Gueni/BLE-NTC/3D/00019202.SLDASM

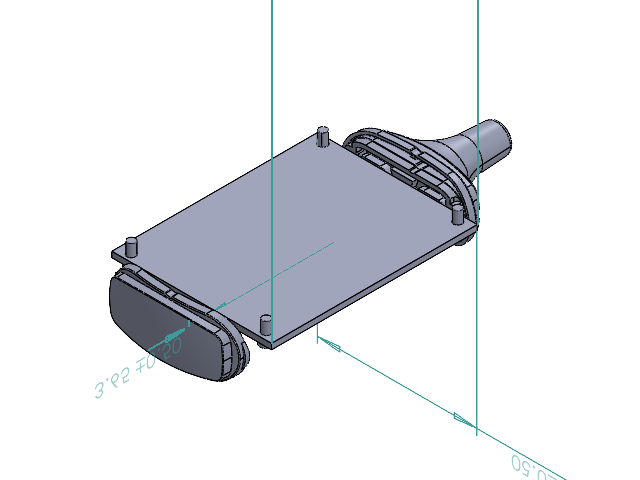
[picture p20: CAD file, 2025-05-13]
3D/00019202.SLDASM
00018026.step
00018023.step
00018713.step
00007817.step x 2
00007874.step x 4
00019221.step
00019614.step
